FabLabKannai/SumobotJr/laser_cutter/body_3mm/README.md

# Body 3mm - Laser Cutter

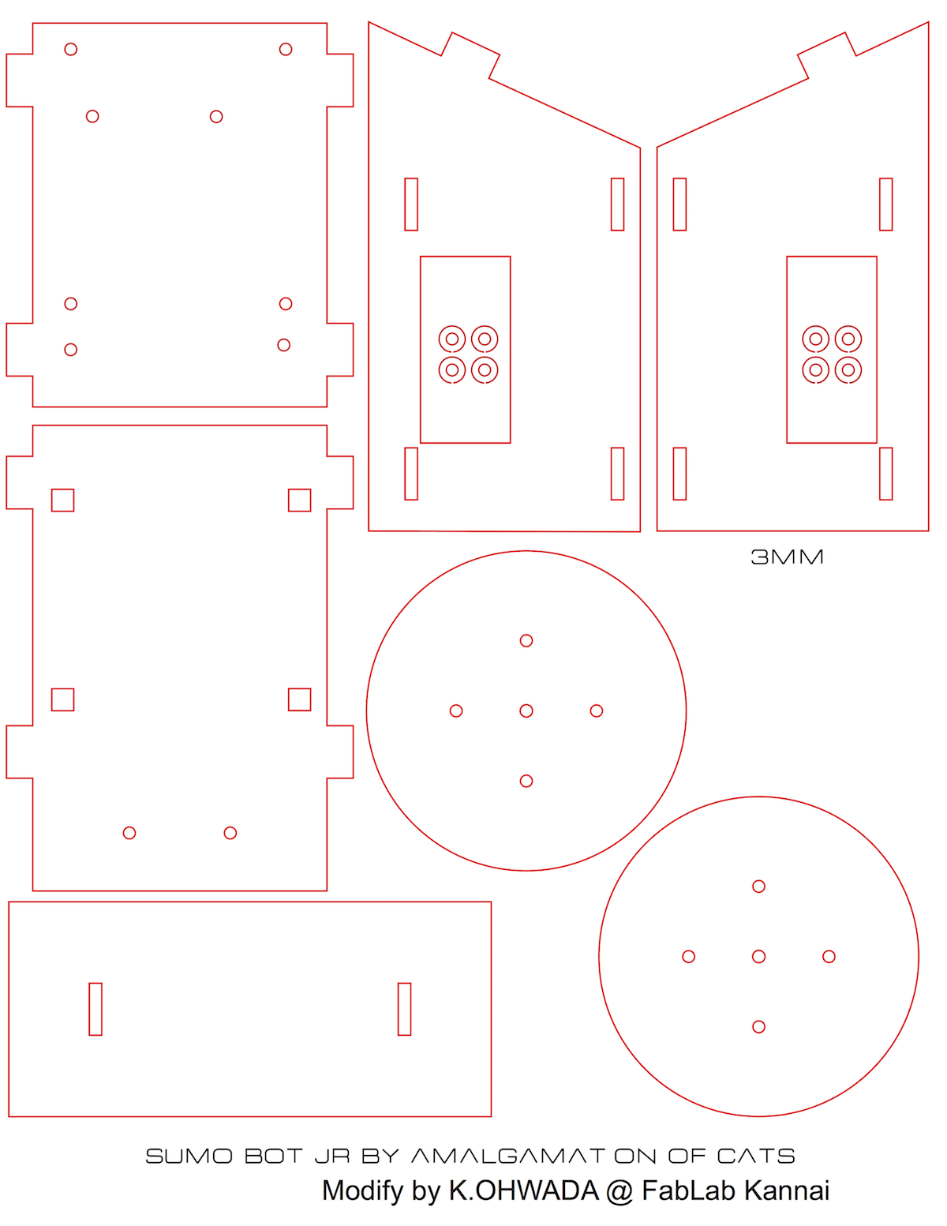
[picture p30: docs/sumbotjr_3mm_custom_ai.png]
  <br/>
