FabLabKannai/SumobotJr/arduino/servo_class/README.md

# servo class - Arduino Skech

Test for Continuous Rotation Servo <br/>
using [Servo class](https://www.arduino.cc/en/Reference/Servo) <br/>
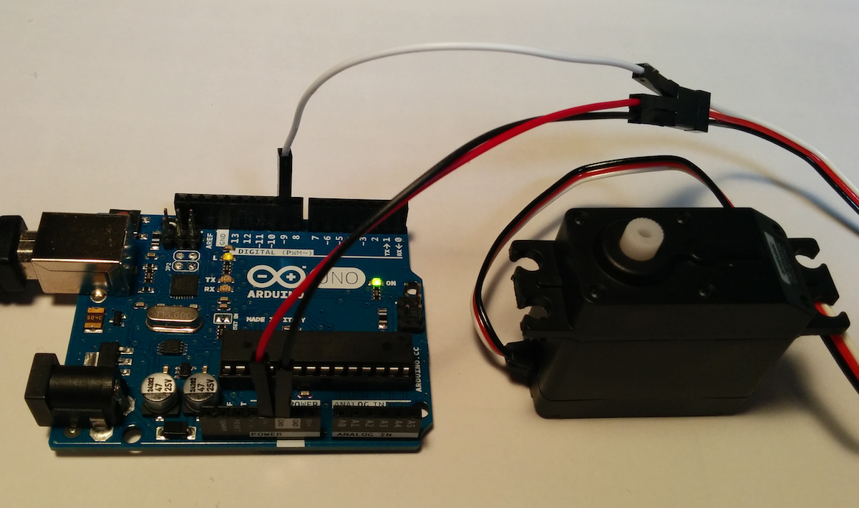
[picture p31: docs/arduino/arduino_servo.png]
 <br/>

### blog (Japanese)
http://android.ohwada.jp/archives/6674
