FabLabKannai/SumobotJr/arduino/servo_command/README.md

# servo command - Arduino Skech

Test for Continuous Rotation Servo <br/>
Command specify forward, backward or etc <br>
 <br/>

### Usage
format : s + three digits <br>
example <br>
- s000 : clockwide full speed <br>
- s080 : clockwide low speed <br>
- s090 : stop <br>
- s100 : anticlockwide low speed <br>
- s180 : anticlockwide full speed <br>

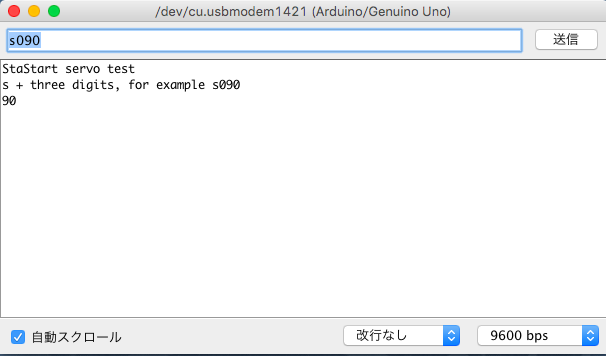
[picture p32: docs/arduino/arduino_servo_command_monitor.png]
 <br/>

### blog (Japanese)
http://android.ohwada.jp/archives/6674
