FabLabKannai/SumobotJr/arduino/servo_digitalwrite/README.md

# servo digitalwrite - Arduino Skech 

Test for Continuous Rotation Servo <br/>
using [digitalWrite](https://www.arduino.cc/en/Reference/DigitalWrite) <br/>
 <br/>

### blog (Japanese)
http://android.ohwada.jp/archives/6674
