FabLabKannai/SumobotJr/arduino/servo_fade/README.md

# servo fade - Arduino Skech

Test for Continuous Rotation Servo <br/>
 <br/>

### Behavior
clockwide <-> stop <-> anticlockwide <br/>
