FabLabKannai/SumobotJr/arduino/sumobot_command/README.md

# sumobot command - Arduino Skech

Test for Sumobot using continuous rotation servos <br>
Command specify forward, backward or etc <br>
 <br/>

### Usage
command format : one ASCII charactor <br>
- 0 : LED off <br>
- 1 : LED on <br>
- 2 : LED bilnk <br>
- f : forward <br>
- b : backward <br>
- l : left turn <br>
- r : right turn <br>
- othes : stop <br>

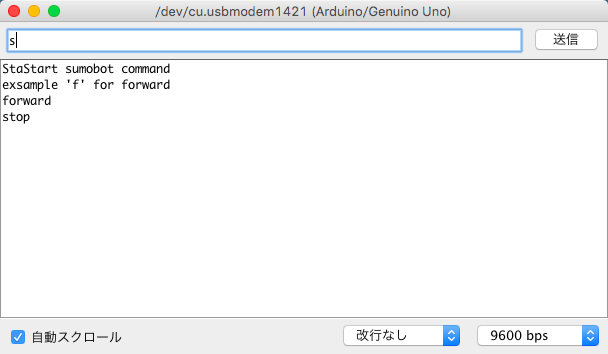
[picture p33: docs/arduino/arduino_sumobot_command_monitor.png]
 <br/>
