FabLabKannai/SumobotJr/raspi/sumobot_daemon/SumobotSample/docs/README.md

Sumobot Controller
===============

Web app to control Sumobot <br>
 <br/>

### Requirements
- OS: Raspbian <br>
- Python 2.7 <br>
- python-dev <br>
$ sudo apt-get install python-dev <br>
- [Virtualenv](https://virtualenv.readthedocs.org/en/latest/) <br>
$ sudo pip install virtualenv <br>

### Install
> $ cd /tmp<br>
$ git clone https://github.com/FabLabKannai/SumobotJr.git <br>
$ mkdir ~/sumobot/ <br>
$ mv SumobotJr/raspi/sumobot_daemon/SumobotSample/ ~/sumobot/ <br>

> $ cd ~/sumobot <br>
$ virtualenv venv <br>
( You do not need to excute this command more than once, if you excuted this at once. ) <br>

> $ source venv/bin/activate <br>
(venv) $ cd SumobotSample <br>
(venv) $ python setup.py install <br>
$ deactivate <br>

you can use service daemon <br>
> $ sudo sh init.sh <br>

### Run
> $ cd ~<br>
$ sudo sumobot/venv/bin/sumobot_sample <br>

or service daemon <br>
> $ sudo /etc/init.d/sumobot-sample start <br>

### Quite service daemon
> $ sudo insserv -r sumobot-sample

### Usage
Access using web browser. <br>
http://IP_ADDR:6010 <br>
