FabLabKannai/SumobotJr/docs/arduino/asm/asm_banding.jpg

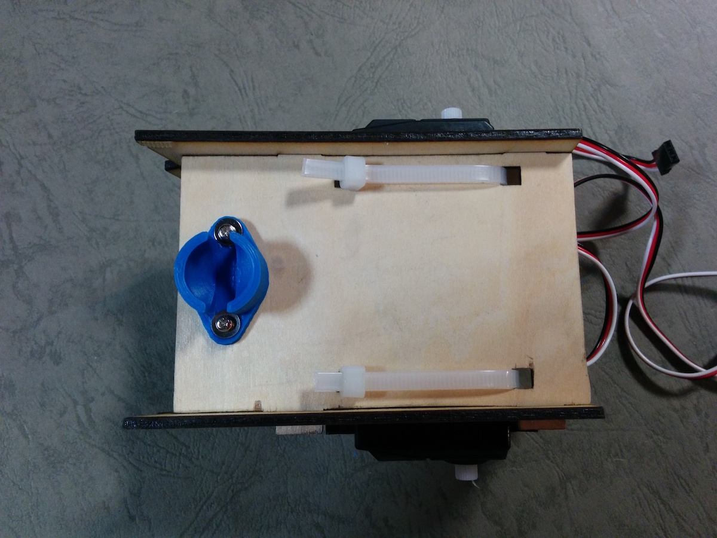
docs/arduino/asm/asm_banding.jpg
