FabLabKannai/SumobotJr/docs/arduino/asm/asm_rubber.jpg

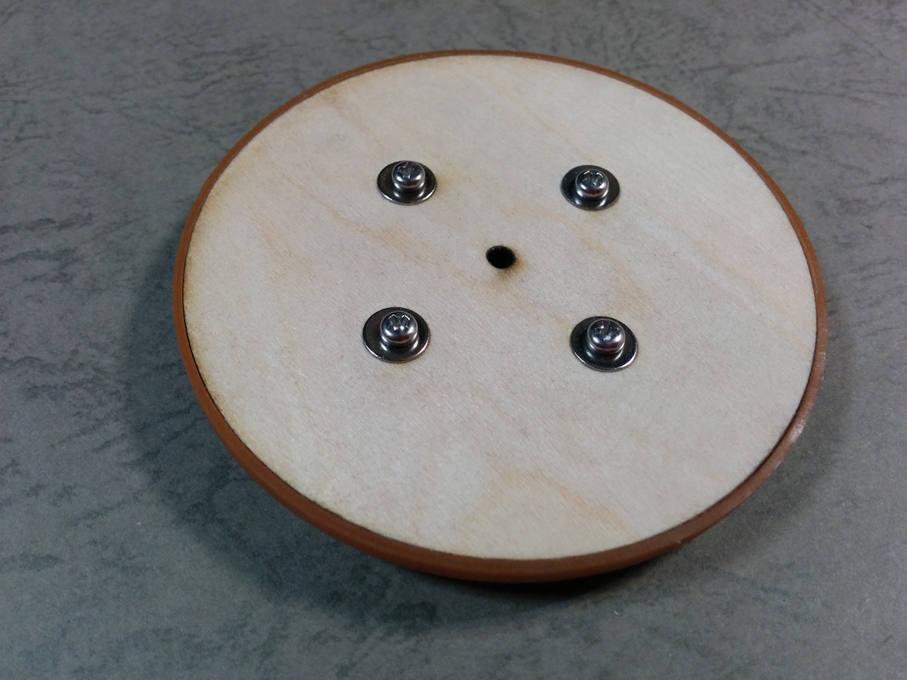
docs/arduino/asm/asm_rubber.jpg
