FabLabKannai/SumobotJr/docs/arduino/asm/asm_servo_mount.jpg

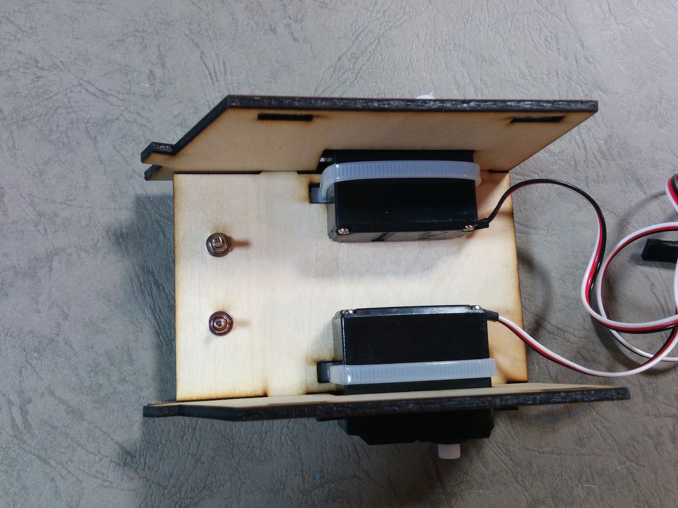
docs/arduino/asm/asm_servo_mount.jpg
