FabLabKannai/SumobotJr/docs/raspi/raspi_circuit.png

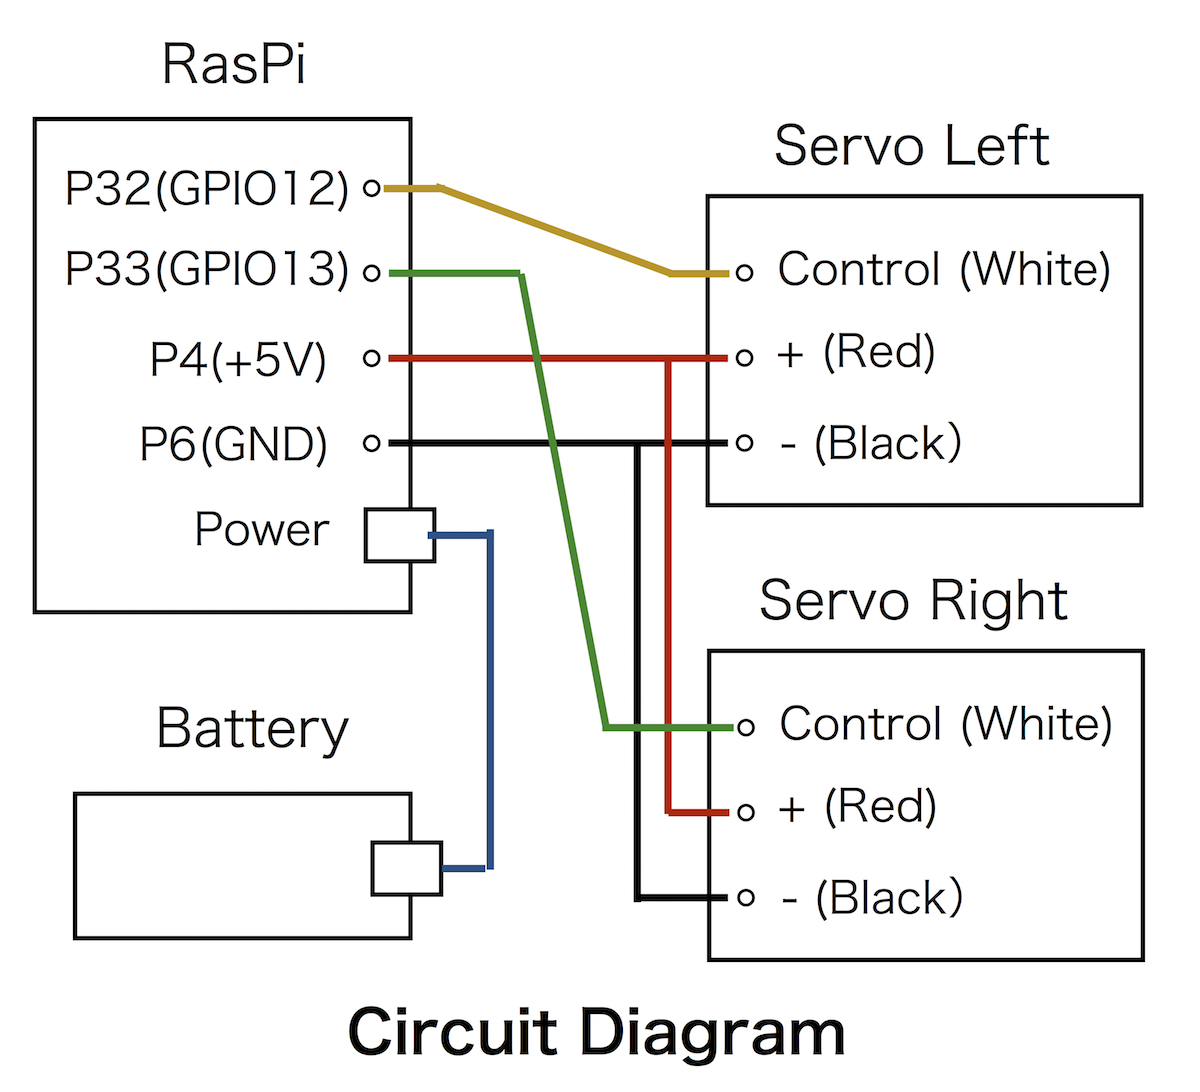
docs/raspi/raspi_circuit.png
