FabLabKannai/SumobotJr/docs/raspi/raspi_servo.jpg

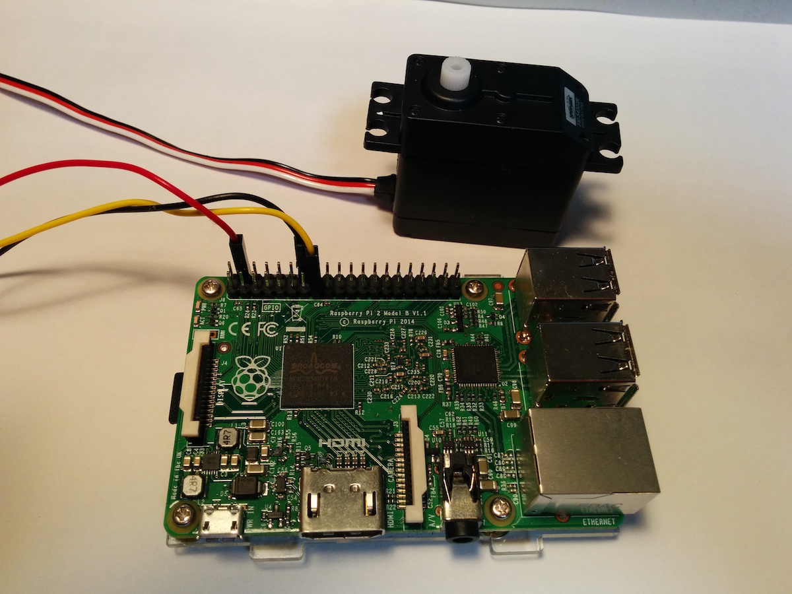
docs/raspi/raspi_servo.jpg
